derpflanz/castle-runner/Firmware/Sound/sound.c

#include <avr/io.h>
#include "sound.h"
#include <avr/interrupt.h>
#include <stdlib.h>

// voice 1 registers
struct note *current_song_voice1;
uint16_t amplitude_voice1;
uint16_t frequency_voice1 = END;
int note_counter_voice1 = -1;
uint8_t *waveform_voice1 = NULL;

// voice 2 registers
struct note *current_song_voice2;
uint16_t amplitude_voice2;
uint16_t frequency_voice2 = END;
int note_counter_voice2 = -1;
uint8_t *waveform_voice2 = NULL;

// waveform values (0-255)
uint8_t sine[] = {
    125, 128, 131, 134, 137, 140, 143, 146, 149, 152, 156, 159, 162, 165, 168, 171, 
    174, 176, 179, 182, 185, 188, 191, 193, 196, 199, 201, 204, 206, 209, 211, 213, 
    216, 218, 220, 222, 224, 226, 228, 230, 232, 234, 236, 237, 239, 240, 242, 243, 
    245, 246, 247, 248, 249, 250, 251, 252, 252, 253, 254, 254, 255, 255, 255, 255, 
    255, 255, 255, 255, 255, 255, 255, 254, 254, 253, 252, 252, 251, 250, 249, 248, 
    247, 246, 245, 243, 242, 240, 239, 237, 236, 234, 232, 230, 228, 226, 224, 222, 
    220, 218, 216, 213, 211, 209, 206, 204, 201, 199, 196, 193, 191, 188, 185, 182, 
    179, 176, 174, 171, 168, 165, 162, 159, 156, 152, 149, 146, 143, 140, 137, 134, 
    131, 128, 124, 121, 118, 115, 112, 109, 106, 103,  99,  96,  93,  90,  87,  84, 81, 
    79, 76, 73, 70, 67, 64, 62, 59, 56, 54, 51, 49, 46, 44, 42, 39, 37, 35, 33, 31, 
    29, 27, 25, 23, 21, 19, 18, 16, 15, 13, 12, 10, 9, 8, 7, 6, 5, 4, 3, 3, 2, 1, 1, 
    0, 0, 0, 0, 0, 0, 0, 0, 0, 0, 0, 1, 1, 2, 3, 3, 4, 5, 6, 7, 8, 9, 10, 12, 13, 15, 
    16, 18, 19, 21, 23, 25, 27, 29, 31, 33, 35, 37, 39, 42, 44, 46, 49, 51, 54, 56, 59, 
    62, 64, 67, 70, 73, 76, 79, 81, 84, 87, 90, 93, 96, 99, 103, 106, 109, 112, 115, 118, 
    121, 124
};

uint8_t triangle[] = {
    2, 4, 6, 8, 10, 12, 14, 16, 18, 20, 22, 24, 26, 28, 30, 32, 34, 36, 38, 40, 42, 
    44, 46, 48, 50, 52, 54, 56, 58, 60, 62, 64, 66, 68, 70, 72, 74, 76, 78, 80, 82, 
    84, 86, 88, 90, 92, 94, 96, 98, 100, 102, 104, 106, 108, 110, 112, 114, 116, 118, 
    120, 122, 124, 126, 128, 130, 132, 134, 136, 138, 140, 142, 144, 146, 148, 150, 
    152, 154, 156, 158, 160, 162, 164, 166, 168, 170, 172, 174, 176, 178, 180, 182, 
    184, 186, 188, 190, 192, 194, 196, 198, 200, 202, 204, 206, 208, 210, 212, 214, 
    216, 218, 220, 222, 224, 226, 228, 230, 232, 234, 236, 238, 240, 242, 244, 246, 
    248, 250, 252, 254, 254, 252, 250, 248, 246, 244, 242, 240, 238, 236, 234, 232, 
    230, 228, 226, 224, 222, 220, 218, 216, 214, 212, 210, 208, 206, 204, 202, 200, 
    198, 196, 194, 192, 190, 188, 186, 184, 182, 180, 178, 176, 174, 172, 170, 168, 
    166, 164, 162, 160, 158, 156, 154, 152, 150, 148, 146, 144, 142, 140, 138, 136, 
    134, 132, 130, 128, 126, 124, 122, 120, 118, 116, 114, 112, 110, 108, 106, 104, 
    102, 100, 98, 96, 94, 92, 90, 88, 86, 84, 82, 80, 78, 76, 74, 72, 70, 68, 66, 64, 
    62, 60, 58, 56, 54, 52, 50, 48, 46, 44, 42, 40, 38, 36, 34, 32, 30, 28, 26, 24, 22, 
    20, 18, 16, 14, 12, 10, 8, 6, 4, 2, 0, 
};

void init_freq_timer_voice_1() {
    // OC0A as output, this is our signal output
    DDRD |= (1 << DDD6);        

    // Connect OC0A: Clear on Compare match, set on BOTTOM
    TCCR0A |= (1 << COM0A1);

    // Fast PWM mode; Runs always from 0x00 to 0xFF
    TCCR0A |= (1 << WGM00) | (1 << WGM01);

    // Clock Select; CS2:0 = 001 -> No prescaling: runs at 16MHz
    TCCR0B |= (1 << CS00);

    // Enable the timer 0 overflow interrupt, causes TIMER0_OVF_vect to actually be called
    TIMSK0 |= (1 << TOIE0);

    // Init compare register
    OCR0A = 0;
}

void init_freq_timer_voice_2() {
    // OC2A as output, this is our signal output
    DDRB |= (1 << DDB3);        

    // Connect OC2A: Clear on Compare match, set on BOTTOM
    TCCR2A |= (1 << COM2A1);

    // Fast PWM mode; Runs always from 0x00 to 0xFF
    TCCR2A |= (1 << WGM20) | (1 << WGM21);

    // Clock Select; CS2:0 = 001 -> No prescaling: runs at 16MHz
    TCCR2B |= (1 << CS20);

    // Enable the timer 0 overflow interrupt, causes TIMER0_OVF_vect to actually be called
    TIMSK2 |= (1 << TOIE2);

    // Init compare register
    OCR2A = 0;
}

void init_duration_timer() {
    // CTC mode (Clear Timer on Compare Match)
    TCCR1B |= (1 << WGM12);  

    // Prescaler 64, gives a speed range on OCR1A between 100 (hyperturbo) and 2000 (very slow)
    TCCR1B |= (1 << CS11)| (1 << CS10);

    // Output Compare A Match Interrupt Enable: calls TIMER1_COMPA_vect
    TIMSK1 |= (1 << OCIE1A);

    // Initialise with a normal speed
    OCR1A = 1000;
}

void set_speed(uint16_t speed) {
    OCR1A = speed;
}

// This sawtooth function is used to calculate a uint8_t value from the, 
// uint16_t frequency, giving us more fine grained frequency steps (0-32768)
// The return value can then be used in another waveform (e.g. sine[])
uint8_t sawtooth_voice1(uint16_t frequency) {
    static uint16_t wvalue = 0;
    wvalue += frequency;

    if (wvalue > 32768) {
        wvalue = 0;
    }
    
    return (uint8_t) (wvalue / 128);
}

uint8_t sawtooth_voice2(uint16_t frequency) {
    static uint16_t wvalue = 0;
    wvalue += frequency;

    if (wvalue > 32768) {
        wvalue = 0;
    }
    
    return (uint8_t) (wvalue / 128);
}

void load_song_voice1(struct note *song) {
    current_song_voice1 = song;
}

void start_song_voice1() {
    note_counter_voice1 = 0;
}

void stop_song_voice1() {
    note_counter_voice1 = -1;
}

void load_song_voice2(struct note *song) {
    current_song_voice2 = song;
}

void start_song_voice2() {
    note_counter_voice2 = 0;
}

void stop_song_voice2() {
    note_counter_voice2 = -1;
}

ISR(TIMER0_OVF_vect) {
    if (note_counter_voice1 < 0) return;

    uint8_t n = sawtooth_voice1(frequency_voice1);

    if (waveform_voice1 != NULL) {
        n = waveform_voice1[n];
    }
    
    uint16_t n_large = n * (amplitude_voice1 / 256);
    n = n_large / 256;
    
    OCR0A = n;
}

ISR(TIMER2_OVF_vect) {
    if (note_counter_voice2 < 0) return;

    uint8_t n = sawtooth_voice2(frequency_voice2);

    if (waveform_voice2 != NULL) {
        n = waveform_voice2[n];
    }
    
    uint16_t n_large = n * (amplitude_voice2 / 256);
    n = n_large / 256;
    
    OCR2A = n;
}

void time_voice1() {
    if (note_counter_voice1 < 0) return;

    static uint16_t attack_step, decay_step, release_step;
    static uint16_t end_of_attack, end_of_decay, end_of_sustain, end_of_release;    
    static uint16_t slice = 0;
    static struct note current_note;
    
    if (slice < end_of_release) {        
        if (slice < end_of_attack) amplitude_voice1 += attack_step; // attack
        if (slice > end_of_attack && slice < end_of_decay) amplitude_voice1 -= decay_step; // decay
        // sustain is just that, nothing changes
        if (slice > end_of_sustain) amplitude_voice1 -= release_step; // release

        slice++;
    } else {
        current_note = current_song_voice1[note_counter_voice1++];

        if (current_note.frequency == END) {
            stop_song_voice1();
        }

        // reset slice and amplitude
        slice = 0;
        amplitude_voice1 = 0;
        frequency_voice1 = current_note.frequency;

        // calculate envelope steps
        attack_step = 65535 / current_note.attack;
        decay_step = 32767 / current_note.decay;
        release_step = 32767 / current_note.release;

        // calculate envelope times
        end_of_attack = current_note.attack;
        end_of_decay = end_of_attack + current_note.decay;
        end_of_sustain = end_of_decay + current_note.sustain;
        end_of_release = end_of_sustain + current_note.release;
    }
}

void time_voice2() {
    if (note_counter_voice2 < 0) return;

    static uint16_t attack_step, decay_step, release_step;
    static uint16_t end_of_attack, end_of_decay, end_of_sustain, end_of_release;    
    static uint16_t slice = 0;
    static struct note current_note;
    
    if (slice < end_of_release) {        
        if (slice < end_of_attack) amplitude_voice2 += attack_step; // attack
        if (slice > end_of_attack && slice < end_of_decay) amplitude_voice2 -= decay_step; // decay
        // sustain is just that, nothing changes
        if (slice > end_of_sustain) amplitude_voice2 -= release_step; // release

        slice++;
    } else {
        current_note = current_song_voice2[note_counter_voice2++];

        if (current_note.frequency == END) {
            stop_song_voice2();
        }

        // reset slice and amplitude
        slice = 0;
        amplitude_voice2 = 0;
        frequency_voice2 = current_note.frequency;

        // calculate envelope steps
        attack_step = 65535 / current_note.attack;
        decay_step = 32767 / current_note.decay;
        release_step = 32767 / current_note.release;

        // calculate envelope times
        end_of_attack = current_note.attack;
        end_of_decay = end_of_attack + current_note.decay;
        end_of_sustain = end_of_decay + current_note.sustain;
        end_of_release = end_of_sustain + current_note.release;
    }
}

ISR(TIMER1_COMPA_vect) {
    time_voice1();
    time_voice2();
}
