derpflanz/castle-runner/Source/castlerunner.asm

; This is the Castle Runner game!
; It uses the cr002-rom.asm library

.orig $8000

cur_row = $C0
cur_col = $C1
steps = $C2
gold = $C3
joy_shadow = $D0
joystick = $D1
level_ptr = $E0

led_blinker = $D2

par1 = $80
par2 = $81

joy_status_pos = $0229

; DATA
copyright = "2026"
gameover = "Game Over!"

; I/O
ddra = $4307
ora_ = $4107

; init
SEI             ; Disable interrupts
CLD             ; Clear "D" flag: use binary mode (instead of BCD)
LDX #$ff        ; Initialise stack on 0x01ff
TXS

; init 6522
LDA #$ff
STA ddra
LDA #$00
STA ora_
STA led_blinker

; init lcd
JSR VIO_ResetDisplay
JSR VIO_InitDisplay
JSR VIO_ClearDisplay
JSR InitVideoRam

; For some strange reason, we need this to correctly clear the video ram (wtf?)
LDA #$00
STA $0200

JSR LoadBackdrop
JSR VIO_WriteGraphScreen

CLI             ; Enable interrupts

; ======================= INITIALISATION ==================================
; initialise location of our runner
LDA #$0F
STA cur_row
LDA #$14
STA cur_col

LDA #$10
STA steps

LDA $4000       ; Joystick shadow
STA joy_shadow

; ======================= GAME LOOP ==================================
GameLoop:
; Read joystick value and store in temp
LDA $4000
STA joystick

; Read joystick value and output to screen (for debug)
LDA #<joy_status_pos
STA par1
LDA #>joy_status_pos
STA par2
LDA joystick
JSR Dec2Ascii

; Print steps
LDA #$4E
STA $80
LDA #$06
STA $81
LDA steps
JSR Dec2Ascii

; Read joystick and change XY for character
LDA $D1           ; When joystick hasn't changed, do nothing
CMP $D0
BEQ GameLoop

LDA $D1
STA $D0

LDA $D1             ; When joy in (or back to) middle, don't do anything
CMP #$FF
BEQ GameLoop

LDA $C0             ; Remove old Runner
STA $94
LDA $C1
STA $95
JSR CalcCharPtr
LDA ' '
JSR WriteChar

LDA $D1
AND #$02            ; UP
BNE Joy1
DEC cur_row
Joy1:
LDA $D1
AND #$04            ; DOWN
BNE Joy2
INC cur_row
Joy2:
LDA $D1
AND #$08            ; LEFT
BNE Joy3
DEC cur_col
Joy3:
LDA $D1
AND #$10            ; RIGHT
BNE Joy4
INC cur_col
Joy4:

LDA cur_row             ; Write new Runner
STA $94
LDA cur_col
STA $95
JSR CalcCharPtr
LDA 'X'
JSR WriteChar

DEC steps
BNE still_alive
LDA #$00
STA $4007           ; play sound
LDA #$0A            ; row 10
STA $94
LDA #$05            ; col 5
STA $95
JSR CalcCharPtr
LDA #<gameover
STA par1
LDA #>gameover
STA par2
JSR WriteString
JSR VIO_WriteCharScreen
JMP dead

still_alive:

LDA led_blinker
EOR #$01
STA ora_
STA led_blinker

JSR VIO_WriteCharScreen
JMP GameLoop

dead:
JMP dead

LoadBackdrop:
    ; Data starting in $C000 is our game backdrop
    ; Load it into the Video RAM
    LDA #$00        ; GraphX = 0
    STA $96

    LDA #$00        ; ($12) = $C000
    STA $12
    LDA #$C0
    STA $13

    WriteXs:
    LDA #$00
    STA $10         ; our count-to-40 counter
    LDA #$C8        ; GraphY = C8 = 200 = top of bottom frame
    STA $97
    JSR CalcGraphPtr

    WriteYs:
    LDA ($12)
    JSR WriteGraph ; This will INC $97

    CLC
    LDA $12
    ADC #$01
    STA $12
    LDA $13
    ADC #$00
    STA $13

    INC $10
    LDA $10
    CMP #$28        ; $28 = 40
    BNE WriteYs
    INC $96
    LDA $96
    CMP #$28
    BNE WriteXs
RTS
