derpflanz/castle-runner/Firmware/EepromProgrammer/include/communication.h

#ifndef __COMMUNICATION_H__
#define __COMMUNICATION_H__

// ASCII convenience defines
#define SOH 0x01
#define STX 0x02
#define ETX 0x03
#define EOT 0x04
#define ENQ 0x05
#define ACK 0x06
#define NAK 0x15
#define SYN 0x16
#define ETB 0x17
#define US  0x1f

// Commands
#define CMD_NOTHING             0x30
#define CMD_WRITE_CODE_EEPROM   0x31
#define CMD_READ_EEPROM         0x32
#define CMD_WRITE_DATA_EEPROM   0x33
#define CMD_ERROR               0x39
#define HEXFILE_MAX_SIZE        32768

#define PRINTLINE { Serial.print("[CR-EP1] "); Serial.println(linebuffer); }
extern char linebuffer[];

class Comm {
    public:
        void setup();
        void printf(char *format, ...);
        byte receiveByte();
        void sendByte(byte b);

    private:

};

extern Comm Communication; 

#endif
