derpflanz/castle-runner/Tools/VirtualCR001/ui.c

#include <ncurses.h>
#include "ui.h"
#include <stdarg.h>
#include <stdlib.h>
#include "debug.h"
#include "generic.h"
#include "fake6502.h"
#include "memory.h"
#include <ctype.h>
#include <string.h>

WINDOW *memory_log, *io_log;
WINDOW *lcd;
WINDOW *memory_win, *rom_win, *stack_win, *video_win, *io_win;

WINDOW *_create_newwin(int height, int width, int starty, int startx)
{	
    WINDOW *local_win;

	local_win = newwin(height, width, starty, startx);
	box(local_win, 0 , 0);		/* 0, 0 gives default characters */
	wrefresh(local_win);		/* Show that box 		*/

	return local_win;
}

char __flag_buf[9];
char *_flags(uint8_t value) {
    unsigned char mask = 1;
    char set, c;
    for (int i = 7; i >= 0; i--) {
        set = (value & mask);
        switch (mask) {
            case FLAG_CARRY:
                c = set?'C':'c';
                break;
            case FLAG_ZERO:
                c = set?'Z':'z';
                break;
            case FLAG_INTERRUPT:
                c = set?'I':'i';
                break;
            case FLAG_DECIMAL:
                c = set?'D':'d';
                break;
            case FLAG_BREAK:
                c = set?'B':'b';
                break;
            case FLAG_CONSTANT:
                c = set?'T':'t';
                break;
            case FLAG_OVERFLOW:
                c = set?'O':'o';
                break;
            case FLAG_SIGN:
                c = set?'S':'s';
                break;
        }

        __flag_buf[i] = c;
        mask <<= 1;
    }
    __flag_buf[8] = '\0';
    return __flag_buf;
}

/* Shows memory in a window, "highlight" will be set blue, the list of addresses in 
   "extra_highlight" will be set red
*/
void _mem_wshow(WINDOW *win, uint8_t *mem, uint16_t base_address, uint16_t highlight, uint16_t *extra_highlights, int stack, int printable) {
    int width, height;
    int direction = stack?-1:1;

    wmove(win, 0, 0);
    getmaxyx(win, height, width);
    uint16_t pointer = base_address;
    int lines = 0;

    wprintw(win, "\n");
    while (lines < (height - 2)) {
        wprintw(win, " [%04x] ", pointer);

        int printable_bytes = (width - 9) / 3;
        for (int i = 0; i < printable_bytes; i++) {
            if (array_contains(pointer, extra_highlights)) {
                wbkgdset(win, COLOR_PAIR(3));
            }
            if (pointer == highlight) {
                wbkgdset(win, COLOR_PAIR(1));
            }
            if (printable == 1 && isprint(mem[pointer])) {
                wprintw(win, "%c ", mem[pointer]);
            } else {
                wprintw(win, "%02x", mem[pointer]);
            }
            wbkgdset(win, COLOR_PAIR(2));
            wprintw(win, " ");
            pointer += direction;
        }
        lines++;
        wprintw(win, "\n");
    }  
}

void _ui_print_io_register(int row, int col, const char *name, uint16_t address, uint8_t *memory, const char * extra) {
    mvwprintw(io_win, row, col, "%s = %02x %08b %s", name, memory[address], memory[address], extra);
}

void _ui_io_registers(uint8_t *memory) {    
    _ui_print_io_register(1, 1, "DDRA", DDRA, memory, "1=OUT, 0=IN");
    _ui_print_io_register(2, 1, "DDRB", DDRB, memory, "1=OUT, 0=IN");

    _ui_print_io_register(1, 40, "PORTA", PORTA, memory, "");
    _ui_print_io_register(2, 40, "PORTB", PORTB, memory, "");
}

void _init_io_log() {
    io_log = _create_newwin(LINES - 10, COLS / 4, 1, COLS / 4);
    scrollok(io_log, TRUE);
    wprintw(io_log, "\n");
    ui_writelog(IOLOG, "Opcode log ready\n");
    wrefresh(io_log);
}

void _init_memory_log() {
    memory_log = _create_newwin(LINES - 10, COLS / 4, 1, 0);
    scrollok(memory_log, TRUE);
    wprintw(memory_log, "\n");
    ui_writelog(MEMLOG, "Memory log ready\n");
    wrefresh(memory_log);
}

void _init_memory_windows() {
    int video_height = 10, stack_height = 5;
    int rom_height = 10, io_height = 5;

    memory_win = _create_newwin(LINES - 2 - rom_height - stack_height - video_height - io_height, COLS / 2, 1, COLS / 2);
    rom_win = _create_newwin(rom_height, COLS / 2, LINES - 1 - stack_height - rom_height - video_height - io_height, COLS / 2);
    stack_win = _create_newwin(stack_height, COLS / 2, LINES - 1 - stack_height - video_height - io_height, COLS / 2);
    video_win = _create_newwin(video_height, COLS / 2, LINES - 1 - video_height - io_height, COLS / 2);
    io_win = _create_newwin(io_height, COLS / 2, LINES - 1 - io_height, COLS / 2);
}

void ui_print_lcd(char character, int row, int column) {
    mvwaddch(lcd, row, column, character);
    wrefresh(lcd);
}

void ui_init_lcd() {
    lcd = newwin(4, 20, LINES - 8, 1);
    wbkgd(lcd, COLOR_PAIR(1));
    wrefresh(lcd);
}

void ui_init() {
    initscr();
    start_color();
    init_pair(1, COLOR_WHITE, COLOR_BLUE);
    init_pair(2, COLOR_WHITE, COLOR_BLACK);
    init_pair(3, COLOR_WHITE, COLOR_RED);
    cbreak();
    noecho();
    nodelay(stdscr, TRUE);
    keypad(stdscr, TRUE);

    printw("F4: Set PORTB; F5: start/stop; F6: reset; F7: IRQ; F8: exit; F10: step; F9: toggle speed");
    refresh();

    _init_memory_log();
    _init_io_log();
    _init_memory_windows();    
}

void ui_clear_log(int target) {
    WINDOW *win = target == IOLOG?io_log:memory_log;

    wclear(win);
    box(win, 0, 0);
    wmove(win, 1, 0);
    wrefresh(win);
}

void ui_writelog(int target, const char *format, ...) {
    WINDOW *win = target == IOLOG?io_log:memory_log;

    char buffer[1024];
    va_list ap;
    va_start(ap, format);
    vsnprintf(buffer, 1024, format, ap);
    va_end(ap);

    wprintw(win, " %s", buffer);
    box(win, 0, 0);
    wrefresh(win);
}

extern uint16_t ea;
void ui_update_ram(uint16_t video_base) {
    uint16_t epoints[2];
    epoints[0] = ea;
    epoints[1] = 0;

    _mem_wshow(memory_win, ram, 0x00, 0, epoints, 0, 0);
    box(memory_win, 0, 0);
    mvwprintw(memory_win, 0, 0, "[ZEROPAGE 0x4000=%02x]", read6502(0x4000));
    wrefresh(memory_win);

    _mem_wshow(rom_win, ram, 0x8000, pc, breakpoints, 0, 0);
    box(rom_win, 0, 0);
    mvwprintw(rom_win, 0, 0, "[ROM PC=%04x A=%02x %08b X=%02x Y=%02x STATUS=%s #=%d TICKS=%d]", 
        pc, a, a, x, y, _flags(status), instructions, clockticks6502);
    wrefresh(rom_win);

    _mem_wshow(stack_win, ram, 0x01ff, (0x0100 | sp), NULL, 1, 0);
    box(stack_win, 0, 0);
    mvwprintw(stack_win, 0, 0, "[STACK SP=01%02x]", sp);
    wrefresh(stack_win);

    _mem_wshow(video_win, ram, video_base, 0x0000, epoints, 0, 1);
    box(video_win, 0, 0);
    mvwprintw(video_win, 0, 0, "[VIDEO]");
    wrefresh(video_win);

    box(io_win, 0, 0);
    mvwprintw(io_win, 0, 0, "[6522 Registers]");
    _ui_io_registers(ram);
    wrefresh(io_win);    
}

void _custom_prompt(const char *msg, char *buf, int max_len) {
    // Create centered prompt window (height 3, width 50)
    WINDOW *win = newwin(5, 50, (LINES - 3) / 2, (COLS - 50) / 2);
    box(win, 0, 0);
    mvwprintw(win, 2, 3, "%s", msg);
    wrefresh(win);
    
    echo();                      // Show typed characters
    curs_set(1);                 // Show cursor
    wgetnstr(win, buf, max_len); // Read input into buf
    noecho();                    // Hide typed characters
    curs_set(0);                 // Hide cursor
    
    delwin(win);
    redrawwin(stdscr);
    refresh();
}

void ui_set_ram(const char *name, uint16_t address) {
    char msg_buf[1024];
    unsigned char value = 0x00;
    snprintf(msg_buf, 1024, "Give new value for %s: ", name);

    char buf[1024];
    _custom_prompt(msg_buf, buf, 10);

    if (strlen(buf) == 8) {
        value = strtoul(buf, NULL, 2);
    } else {
        value = strtoul(buf, NULL, 16);
    }

    ram[address] = value;

    ui_writelog(IOLOG, "Set value of %s to %s (%02x)\n", name, buf, value);
}
